PaulW/rp2040-keyboard-converter/docs/scancodes/set1.md

# Scancode Set 1 (XT)

Scancode Set 1 is the scancode design used by IBM PC and PC/XT keyboards. The designation "XT scancode set" derives from its use in the PC/XT keyboard. Set 1 continues to be used by keyboards operating in XT compatibility mode or implementing XT protocol support.

The encoding scheme: each key generates a make code when pressed and a break code when released. Break codes use the make code with bit 7 set (adding 0x80). Extended keys require multibyte sequences using E0 and E1 prefixes to encode keys not present on the original XT keyboard layout. Set 1 has been in use since the original IBM PC/XT era and remains supported in XT compatibility modes.

## Encoding Scheme

### Basic Encoding

Set 1 uses an 8-bit encoding where:

- **Bit 7 (0x80)**: Release flag
  - `0` = Key press (make code)
  - `1` = Key release (break code)
- **Bits 6-0**: Key identity (0x01-0x7F)

### Make and Break Codes

| Event | Encoding | Example (ESC key = 0x01) |
| --- | --- | --- |
| **Key Press (Make)** | `code` | `0x01` |
| **Key Release (Break)** | `code \| 0x80` | `0x81` |

This simple scheme means:

- Make code: `0x1C` (Return key pressed)
- Break code: `0x9C` (Return key released)

### Extended Keys (E0 Prefix)

The IBM Enhanced Keyboard (introduced with the IBM AT) added keys not present on the original XT keyboard: arrow keys, separate cursor movement keys (Home, End, Page Up, Page Down), and additional modifiers (Right Alt, Right Control). IBM used the E0 prefix byte to encode these "extended keys" in a separate namespace from the existing single-byte scancodes.

Extended keys use a two-byte sequence:

| Sequence | Description |
| --- | --- |
| `E0 xx` | Extended key press |
| `E0 (xx \| 0x80)` | Extended key release |

**Example: Right Control**

- Press: `E0 1D`
- Release: `E0 9D`

Extended keys include:

- Right Alt, Right Control
- Arrow keys (Up, Down, Left, Right)
- Navigation cluster (Home, End, Page Up, Page Down, Insert, Delete)
- Windows keys (E0 5B, E0 5C)
- Application key (E0 5D)
- Multimedia keys

### Pause/Break Key (E1 Prefix)

The Pause/Break key sends a 6-byte sequence entirely on key-down. There is no key-up wire event.

| Event | Sequence |
| --- | --- |
| **Pause key-down** (press only) | `E1 1D 45 E1 9D C5` (no separate key-up wire event) |
| **Break make** (Ctrl+Pause) | `E0 46` (some keyboards emit `E0 45`) |
| **Break release** (Ctrl+Pause)  | `E0 C6` (some keyboards emit `E0 C5`) |

**Important**:

- The Pause key has no separate key-release event on the wire. The full 6-byte sequence `E1 1D 45 E1 9D C5` arrives on key-down only. The converter uses `E1 1D 45` to generate a HID press and `E1 9D C5` to generate a HID release — both are derived from the single key-down burst, not from separate wire events.
- Break (Ctrl+Pause) is a standard make/release pair. Some keyboards emit `E0 45`/`E0 C5` instead of `E0 46`/`E0 C6`.

**USB HID Mapping:**

- All Pause variants map to **interface code 0x48** (USB HID Pause/Break key)
- E1 Pause: `E1 1D 45` → 0x48 press; `E1 9D C5` → 0x48 release (both from single key-down burst; no Ctrl modifier)
- E0 46 or E0 45 (Ctrl+Pause make): → 0x48 make, with Ctrl asserted in the modifier byte (Ctrl is physically held when this sequence is sent)
- E0 C6 or E0 C5 (Ctrl+Pause release): → 0x48 release, with Ctrl still in the modifier byte
- See Issue #21 for historical context on E0 mapping fixes
- Note: Some very old or non-compliant keyboards may not emit the E1 prefix for Pause
  (they instead send a bare sequence that looks like Ctrl+NumLock). Such keyboards cannot
  be reliably distinguished from intentional Ctrl+key combinations in firmware without
  introducing fragile heuristics that break other combinations. Recommended workaround:
  remap an unused physical key (for example Scroll Lock) to PAUS in your keyboard
  configuration if you need a dedicated Pause key for a non-compliant keyboard.

### Fake Shift Codes

Set 1 Print Screen scancodes include "fake shift" codes. The IBM PC XT Technical Reference documents Print Screen as involving the Shift key. The AT keyboard's Print Screen implementation uses extended key encoding (E0 prefix) and includes shift codes in the scancode sequence that do not correspond to physical Shift key presses.

Implementations must filter these fake shift codes to prevent unintended Shift key events in the output.

Set 1 Print Screen sequences include "fake shift" codes:

| Sequence | Description |
| --- | --- |
| `E0 2A E0 37` | Print Screen press (fake left shift + actual code) |
| `E0 B7 E0 AA` | Print Screen release (actual release + fake left shift release) |

**Fake shift bytes to ignore:**

- `E0 2A` - Fake Left Shift press
- `E0 AA` - Fake Left Shift release
- `E0 36` - Fake Right Shift press
- `E0 B6` - Fake Right Shift release

Modern converters should **filter out** these fake shift codes to prevent spurious Shift events.

### Self-Test Code Collision

Set 1 has a collision between self-test codes and valid scancodes. The self-test passed code `0xAA` is identical to the Left Shift break code (`0x2A | 0x80 = 0xAA`). This creates a potential for misinterpreting keyboard reset events as key releases.

**Protocol Layer Filtering:**

The collision is mitigated by protocol-layer filtering during keyboard initialisation. The protocol layer (XT, AT/PS2) consumes self-test codes before they reach the scancode processor:

- **XT Protocol**: Filters `0xAA` (BAT_PASSED) and `0xFC` (BAT_FAILED) whilst in `UNINITIALISED` state—only after receiving `0xAA` does it transition to `INITIALISED` and begin forwarding scancodes to the ring buffer (see [`src/protocols/xt/keyboard_interface.c`](../../src/protocols/xt/keyboard_interface.c))
- **AT/PS2 Protocol**: Expects `0xAA` (BAT_PASSED) in `INIT_AWAIT_SELFTEST` state—any other byte triggers a reset sequence; only after successful self-test does it transition to `INIT_READ_ID_1` and eventually `INITIALISED` (see [`src/protocols/at-ps2/keyboard_interface.c`](../../src/protocols/at-ps2/keyboard_interface.c))
- Once `INITIALISED`, all codes are forwarded unchanged to the scancode layer via the ring buffer—no protocol-layer filtering

**Scancode Layer Behaviour:**

The Set 1 scancode processor ([`src/scancodes/set1/scancode.c`](../../src/scancodes/set1/scancode.c)) does **not** filter self-test codes. It performs a range check (`if (code <= 0xD8)`) that processes all valid scancodes, including `0xAA`:

Since `0xAA` (170 decimal) is less than `0xD8` (216 decimal), it would be processed as a normal Left Shift break code if received post-initialisation. The scancode processor comment explicitly notes: _"Self-test codes (0xAA) are handled by protocol layer during initialisation"_ (see [`src/scancodes/set1/scancode.c`](../../src/scancodes/set1/scancode.c)).

The only special handling of `0xAA` in the scancode layer occurs in the E0-prefixed state, where it's filtered as a "fake shift" sequence for Print Screen (not because it's a self-test code):

```c
case E0:
    switch (code) {
        case 0x2A:
        case 0xAA:  // Filtered as fake shift, NOT as self-test code
        case 0x36:
        case 0xB6:
            // ignore fake shift
            state = INIT;
            break;
```

**Why Protocol-Layer Filtering Suffices:**

Protocol-layer filtering during initialisation is the sole mitigation for self-test code collisions. Post-initialisation, keyboards should not spontaneously send `0xAA` during normal operation. If hot-plugging occurs (not a supported scenario), the `0xAA` would indeed be misinterpreted as Left Shift break.

## State Machine

Set 1 requires a **5-state** state machine to handle all sequences:

```text
┌─────────────┐
│    INIT     │ ◄─────────────────┐
└─────┬───────┘                   │
      │                           │
      ├─[E0]──► E0 ──[code]───────┤
      │                           │
      ├─[E1]──► E1 ──[1D]──► E1_1D ──[45]──────────────────────────────────┐
      │          └───[9D]──► E1_9D ──[C5]────────────────────────────────┐ │
      │                                                                  │ │
      └─[code]───────────────────────────────────────────────────────────┘ │
                                                                           │
      ◄────────────────────────────────────────────────────────────────────┘
```

### State Descriptions

| State | Description | Next Action |
| --- | --- | --- |
| **INIT**  | Waiting for scancode | Process code or enter prefix state |
| **E0** | E0 prefix received | Process extended key, filter fake shifts |
| **E1** | E1 prefix received | Begin Pause sequence parsing |
| **E1_1D** | E1 1D received | Expect 45 (Pause make), then return to INIT |
| **E1_9D** | E1 9D received | Expect C5 (Pause release), then return to INIT |

## Key Characteristics

**What works well:**

The encoding is quite simple—release codes are just make codes with 0x80 added, which makes the state machine fairly compact at only 5 states. Single-byte scancodes are the norm, which keeps things efficient. Each byte has semantic meaning, so the protocol is self-synchronising. BIOS implementations support Set 1 widely, so compatibility's rarely an issue.

**Where it gets awkward:**

The keyspace is limited to 128 make codes (7-bit), which becomes a problem for modern keyboards with extra keys. Print Screen requires filtering out "fake shift" codes that were added for compatibility. The Pause/Break key uses an irregular sequence—6 bytes for Pause, and the break code doesn't follow the usual pattern. If you're using the XT protocol, there's no way for the host to talk back to the keyboard—it's strictly one-way communication.

## Code Range

| Range | Usage |
| --- | --- |
| `0x01-0x53` | Standard key make codes (83-key XT) |
| `0x54-0x56` | Reserved/extended make codes |
| `0x57-0x58` | F11/F12 make codes (101-key extension) |
| `0x59-0x7F` | Reserved/extended |
| `0x81-0xD3` | Standard key break codes (83-key XT, make + 0x80) |
| `0xD4-0xD6` | Reserved/extended break codes |
| `0xD7-0xD8` | F11/F12 break codes (101-key extension, make + 0x80) |
| `0xD9-0xFF` | Reserved/extended break codes |

## Special Codes

| Code | Description |
| --- | --- |
| `0xAA` | Self-test passed (BAT - Basic Assurance Test) [⚠️ Collision](#self-test-code-collision) |
| `0xE0` | Extended key prefix |
| `0xE1` | Pause/Break prefix |
| `0xEE` | Echo response (not used in XT) |
| `0xF0` | Reserved |
| `0xFA` | ACK (not used in XT) |
| `0xFC` | Self-test failed [⚠️ Collision](#self-test-code-collision) |
| `0xFE` | Resend (not used in XT) |
| `0xFF` | Error/Buffer overflow |

## Example Sequences

### Regular Key (ESC)

```yaml
Press: 01
Release: 81
```

### Extended Key (Right Arrow)

```yaml
Press: E0 4D
Release: E0 CD
```

### Print Screen (with fake shifts)

```text
Press:   E0 2A E0 37  (filter E0 2A, process E0 37)
Release: E0 B7 E0 AA  (process E0 B7, filter E0 AA)
```

### Pause/Break

```text
Pause (make):    E1 1D 45  (fires on keypress)
Pause (release): E1 9D C5  (fires immediately after, same physical press)
Break (make):    E0 46     (Ctrl+Pause down)
Break (release): E0 C6     (Ctrl+Pause up)
```

## Implementation Notes

### Processing Algorithm

```c
// Simplified Set 1 processing
switch (state) {
    case INIT:
        if (code == 0xE0) {
            state = E0;
        } else if (code == 0xE1) {
            state = E1;
        } else {
            bool is_release = (code & 0x80) != 0;
            uint8_t key = code & 0x7F;
            handle_key(key, !is_release);
        }
        break;

    case E0:
        // Filter fake shifts: 2A, AA, 36, B6
        if (code != 0x2A && code != 0xAA &&
            code != 0x36 && code != 0xB6) {
            bool is_release = (code & 0x80) != 0;
            uint8_t key = translate_e0_key(code & 0x7F);
            handle_key(key, !is_release);
        }
        state = INIT;
        break;

    case E1:
        // Pause sequence handling...
        break;
}
```

### Translation Requirements

E0-prefixed keys require translation to their logical key codes:

- Map extended scancodes to appropriate HID usage codes
- Handle duplicate keys (e.g., both Left and Right Control)
- Distinguish between main keyboard and numeric keypad keys

### Compatibility Considerations

1. **XT Protocol**: Unidirectional, no host-to-keyboard commands
2. **No LED Control**: XT keyboards have built-in LED logic, not host-controlled
3. **No Typematic Control**: Key repeat rate is keyboard-internal
4. **Self-Test Code Handling**: Protocol-layer filtering during initialisation prevents self-test code collision (see [Self-Test Code Collision](#self-test-code-collision))

## Performance Characteristics

- **Bytes per key action**: 1 byte per make/break event; 2 bytes for a standard press+release pair. Extended sequences are longer.
- **State machine complexity**: Medium (5 states)
- **Processing overhead**: Low (simple bit manipulation)
- **Memory requirements**: ~256 bytes for E0 translation table

## Keyboards Using Set 1

- IBM PC/XT keyboards (1981-1987)
- IBM Model F XT (Part 1501100, 1501105)
- Some early IBM Model M keyboards with XT interface
- Many modern mechanical keyboards in "XT mode"
- Cherry G80 series with XT interface

**Note**: XT keyboards don't respond to keyboard ID commands (0xF2) because the protocol is unidirectional (keyboard to host only).

## Source Code

- **[`scancode.h`](../../src/scancodes/set1/scancode.h)** - Set 1 processor interface
- **[`scancode.c`](../../src/scancodes/set1/scancode.c)** - State machine implementation
- **[Unified Processor](../../src/scancodes/set123/)** - Multi-set processor including Set 1

## References

- [IBM PC/XT Technical Reference Manual (1983)](http://bitsavers.org/pdf/ibm/pc/xt/)
- [IBM Personal Computer AT Technical Reference (1984)](http://bitsavers.org/pdf/ibm/pc/at/1502494_PC_AT_Technical_Reference_Mar84.pdf)
- [tmk Keyboard Wiki - XT Keyboard Protocol](https://github.com/tmk/tmk_keyboard/wiki/IBM-PC-XT-Keyboard-Protocol)
- [IBM Model F XT - VintagePC](https://www.seasip.info/VintagePC/ibm_1501105.html)

---

## Related Documentation

- [XT Protocol](../protocols/xt.md) - Protocol specification using Scancode Set 1
- [Protocols Overview](../protocols/README.md) - All supported protocols
- [Architecture](../advanced/README.md) - System architecture and scancode processing

---

**Questions or stuck on something?**
Use [GitHub Discussions](https://github.com/PaulW/rp2040-keyboard-converter/discussions) or [open an issue](https://github.com/PaulW/rp2040-keyboard-converter/issues) if you've found a problem.
