PaulW/rp2040-keyboard-converter/tools/README.md

# Development Tools

The tools in this directory handle enforcement, static analysis, and testing for the RP2040 Keyboard Converter project:

- **`lint.sh`** — fast pre-commit checks for architectural rule violations (blocking ops, IRQ safety, naming conventions, etc.)
- **`analyse.sh`** — deeper language-level analysis via Clang-Tidy and Cppcheck, run inside Docker against fully-built artefacts
- **`filter_compile_db.py`** / **`parse_compile_db.py`** — helper scripts used by `analyse.sh` to process the cmake compilation database
- **`test-enforcement.sh`** — meta-testing suite for validating the lint checks themselves

## lint.sh

This script checks source code against the architectural rules defined in `.github/copilot-instructions.md`.

### Usage

```bash
# Run locally (warnings don't fail)
./tools/lint.sh

# Run in strict mode (warnings cause failure, used in CI)
./tools/lint.sh --strict
```

### What It Checks

The script runs through nineteen different checks, each targeting a specific architectural rule:

1. **Blocking Operations** - Detects `sleep_ms()`, `sleep_us()`, `busy_wait_us()`, `busy_wait_ms()`
   - ❌ **Fails**: Any blocking call found in src/
   - 💡 **Fix**: Use time-based state machines with `to_ms_since_boot(get_absolute_time())`
   - 💡 **Suppress error**: Add `// LINT:ALLOW blocking` comment for debug-only code with IRQ protection

1. **Multicore API Usage** - Detects `multicore_launch_core1`, `multicore_fifo_*`
   - ❌ **Fails**: Any multicore API usage
   - 💡 **Fix**: This project is single-core only (Core 0) by design

1. **printf in IRQ Context** - Heuristic check for `printf` in `__isr` functions
   - ⚠️ **Warns**: Possible printf/fprintf/sprintf in interrupt handlers
   - 💡 **Fix**: Use `LOG_*` macros (allowed - designed for IRQ use) or defer logging to main loop

1. **ringbuf_reset() Usage** - Detects calls to `ringbuf_reset()`
   - ⚠️ **Warns**: Must only be called with IRQs disabled
   - 💡 **Fix**: Only use during initialisation or state machine resets
   - 💡 **Suppress warning**: Add `// LINT:ALLOW ringbuf_reset` comment on same line

1. **docs-internal/ in Repository** - Checks for committed internal docs
   - ❌ **Fails**: Any docs-internal/ files tracked by git
   - 💡 **Fix**: These are local-only, never commit them

1. **copy_to_ram Configuration** - Verifies code runs from RAM
   - ⚠️ **Warns**: `pico_set_binary_type(copy_to_ram)` not found
   - 💡 **Fix**: Add to CMakeLists.txt for timing-critical code
   - 🔧 **Runtime check**: Debug builds include `ram_check_verify()` - panics if executing from Flash

1. **IRQ-Shared Variables** - Comprehensive volatile and memory barrier analysis
   - ⚠️ **Warns**: Static variables accessed in `__isr` functions without `volatile` keyword
   - ⚠️ **Warns**: Volatile reads/writes without surrounding `__dmb()` memory barriers
   - 💡 **Fix**: Use `volatile` + `__dmb()` for IRQ/main shared data
   - 💡 **Suppress warning**: Add `// LINT:ALLOW non-volatile` or `// LINT:ALLOW barrier` with justification

1. **Tab Characters** - Enforces spaces-only indentation
   - ❌ **Fails**: Tab characters found in source files
   - 💡 **Fix**: Use 4 spaces, never tabs (run `expand -t 4 <file>` to convert)

1. **Header Guards** - Verifies `#ifndef`/`#define` guards in .h files
   - ⚠️ **Warns**: Header files missing include guards
   - 💡 **Fix**: Add `#ifndef FILENAME_H` / `#define FILENAME_H` / `#endif` pattern

1. **File Headers** - Checks for license headers
   - ⚠️ **Warns**: Source files missing GPL or MIT license headers
   - 💡 **Fix**: Add appropriate license header (see code-standards.md for template)

1. **Naming Conventions** - Detects camelCase (expects snake_case)
   - ⚠️ **Warns**: Possible camelCase function/variable names
   - 💡 **Fix**: Use snake_case (e.g., `keyboard_interface_task`, not `keyboardInterfaceTask`)

1. **Include Order** - Validates include directive organisation
   - ⚠️ **Warns**: Own header not first, or SDK headers after project headers
   - 💡 **Fix**: Order: own header → blank line → stdlib → Pico SDK → external libs → project headers

1. **Missing __isr Attribute** - Checks interrupt handler declarations
   - ⚠️ **Warns**: Functions named `*_irq_handler` without `__isr` attribute
   - 💡 **Fix**: Use `void __isr keyboard_irq_handler(void)` for interrupt handlers

1. **Compile-Time Validation** - Advisory check for `_Static_assert` and `#error`
   - ℹ️ **Info**: Reports presence of compile-time validation directives
   - 💡 **Suggestion**: Consider adding compile-time checks for constants (see code-standards.md)
   - 📝 **Note**: This is advisory-only and doesn't affect pass/fail status

1. **Protocol Setup Consistency (Ring Buffer)** - Validates keyboard protocol setup pattern
   - ⚠️ **Warns**: Missing `ringbuf_reset()` call in `keyboard_interface_setup()` (keyboard protocols only)
   - 💡 **Fix**: Add `ringbuf_reset()` before PIO/IRQ setup as part of the standard 13-step initialisation
   - 📝 **Note**: Mouse protocols excluded (direct event processing, no ring buffer)
   - 📚 **Reference**: See [Protocol Implementation Guide](../docs/development/protocol-implementation.md)

1. **Protocol Setup Consistency (PIO IRQ Dispatcher)** - Validates centralised PIO IRQ management
   - ❌ **Fails**: Direct `irq_set_priority()` calls in protocol code (deprecated pattern)
   - ⚠️ **Warns**: Missing `pio_irq_dispatcher_init()` call in protocol setup functions
   - 💡 **Fix**: Use centralised PIO IRQ dispatcher from pio_helper subsystem
     - Call `pio_irq_dispatcher_init(pio_engine.pio)` during setup
     - Call `pio_irq_register_callback(&handler_function)` to register protocol handler
     - Do NOT call `irq_set_priority()` directly in protocols (managed centrally)
   - 📝 **Note**: Ensures proper IRQ multiplexing for multi-device support (e.g., keyboard + mouse)
   - 📚 **Reference**: See [src/common/lib/pio_helper.h](../src/common/lib/pio_helper.h) for API documentation

1. **Indentation Consistency** - Enforces 4-space indentation (detects 2-space)
   - ❌ **Fails**: Files with more than 5 lines using 2-space indentation
   - 💡 **Fix**: Use 4-space indentation consistently throughout the codebase
   - 📝 **Note**: clang-format off/on blocks are excluded from this check
   - 🔧 **Reference**: See [Code Standards](../docs/development/code-standards.md#formatting-and-style) for indentation rules

1. **Trailing Whitespace** - Detects lines ending with spaces
   - ❌ **Fails**: Any `.c` or `.h` file in `src/` with any trailing whitespace
   - ❌ **Fails**: Any `.md` file in `docs/`, `tools/`, `src/`, or root with a single trailing space
   - 💡 **Fix**: Configure your editor to strip trailing whitespace on save, or run `sed -i 's/[[:space:]]*$//' <file>`
   - 📝 **Note**: Trailing whitespace causes noisy diffs and editor warnings
   - 📝 **Note**: Double trailing spaces in Markdown files are intentionally allowed — they produce a hard line break (`<br>`)

1. **Local Const Hex-Literal Variables** - Detects hex-literal magic numbers hidden in `const` variable declarations
   - ❌ **Fails**: Any `const TYPE var = 0x...` declaration inside a function body
   - 💡 **Fix**: Move the value to a file-scope `#define` in the relevant constants block
   - 📝 **Note**: `readability-magic-numbers` in clang-tidy treats `const TYPE var = LITERAL` as "introducing a named constant" and never fires on such declarations — this check closes that gap
   - 📝 **Note**: Suppress with `// LINT:ALLOW local-const-hex` and a justification comment if absolutely necessary

### Integration

- **Pre-commit**: Recommended to run before committing
- **CI**: Automatically runs in strict mode on all PRs
- **Local development**: Run periodically during development

### Example Output

```text
========================================
RP2040 Architecture Lint Checks
========================================

[1/19] Checking for blocking operations...
✓ No blocking operations found

[2/19] Checking for multicore API usage...
✓ No multicore API usage found

...

========================================
Lint Summary
========================================
✓ All checks passed!
```

### Common Issues and Fixes

#### Blocking Operations Detected

**Problem**: Code uses `sleep_ms(100)` for timing

**Fix**: Use time-based state machine
```c
// Before (blocking)
sleep_ms(100);
do_something();

// After (non-blocking)
static uint32_t start_time = 0;
static bool waiting = false;

if (!waiting) {
    start_time = to_ms_since_boot(get_absolute_time());
    waiting = true;
    return;
}

if (to_ms_since_boot(get_absolute_time()) - start_time >= 100) {
    do_something();
    waiting = false;
}
```

**Exception**: Debug-only code with explicit justification
```c
// Acceptable use case: UART debug logging with IRQ protection
if (in_irq()) {
    return !queue_full();  // Never block in IRQ
}
sleep_us(delay_us);  // LINT:ALLOW blocking - UART debug logging only, IRQ-protected, yields CPU for PIO/interrupts
```

#### printf in IRQ Context

**Problem**: `printf()` called in interrupt handler

**Fix**: Use LOG macros or defer
```c
// Before (unsafe)
void __isr keyboard_irq_handler(void) {
    printf("Key pressed\n");  // DMA conflict!
}

// After (safe)
void __isr keyboard_irq_handler(void) {
    LOG_DEBUG("Key pressed");  // IRQ-safe
}

// Or defer to main loop
static volatile bool key_pressed = false;

void __isr keyboard_irq_handler(void) {
    key_pressed = true;
    __dmb();
}

void main_loop(void) {
    if (key_pressed) {
        __dmb();
        printf("Key pressed\n");
        key_pressed = false;
    }
}
```

#### Suppressing ringbuf_reset Warnings

**Problem**: Legitimate `ringbuf_reset()` call during initialisation triggers warning

**Fix**: Add annotation comment
```c
// Legitimate use - IRQs not yet enabled during init
void keyboard_interface_init(void) {
    // ... setup code ...
    ringbuf_reset();  // LINT:ALLOW ringbuf_reset
}
```

The lint script will skip warnings for lines with the `// LINT:ALLOW ringbuf_reset` annotation.

### Runtime RAM Execution Check

Debug builds (`cmake -DCMAKE_BUILD_TYPE=Debug`) include a runtime verification that code is actually executing from SRAM:

```c
#include "ram_check.h"

int main(void) {
    ram_check_verify();  // Panics if executing from Flash (0x10000000)
                          // Passes if executing from SRAM (0x20000000)
    // ... rest of initialisation
}
```

This catches Flash execution at runtime, which complements the lint script's static check for `pico_set_binary_type(copy_to_ram)` in CMakeLists.txt.

## Testing the Tools

If you're modifying the enforcement tools themselves (not regular development), run the meta-testing suite:

```bash
./tools/test-enforcement.sh
```

This validates that lint checks detect violations correctly. See [TESTING.md](TESTING.md) for detailed scenarios and [QUICKTEST.md](QUICKTEST.md) for quick reference commands.

For regular development, just run the lint script before committing:

```bash
./tools/lint.sh && echo "✅ Ready to commit"
```

For deeper language-level analysis, run the analyser after a build:

```bash
docker compose run --rm -e KEYBOARD="modelf/pcat" analyser
```

## analyse.sh

This script runs the Debian Packaged version of [Clang 19.1.7](https://discourse.llvm.org/t/llvm-19-1-7-released/84062) and [Cppcheck 2.19.0](https://cppcheck.sourceforge.io/) against the project's source files. Running the analyser locally lets you reproduce and investigate any static-analysis findings before they appear in code review.

The analyser is invoked via the `analyser` Docker Compose service, which runs a full firmware build first and then analyses the result. Because analysis runs against the completed build artefacts — including all generated PIO header files — there are no missing-file or linking errors that you'd otherwise see if analysis ran before the build.

### Usage

```bash
# Build + analyse (recommended — uses fully built artefacts)
docker compose run --rm -e KEYBOARD="modelf/pcat" analyser

# With a different keyboard configuration
docker compose run --rm -e KEYBOARD="modelm/enhanced" analyser

# With mouse support included
docker compose run --rm -e KEYBOARD="modelm/enhanced" -e MOUSE="at-ps2" analyser
```

`KEYBOARD` selects which keyboard configuration cmake uses when building. It defaults to `modelf/pcat` if not set, which exercises the AT/PS2 protocol, HID interface, scancode processing, and Command Mode — the most common code paths.

### What It Checks

**Clang-Tidy** runs a set of checks focused on correctness and readability for embedded C11 code. C++-specific and modernise checks are disabled. The active checks are configured in [`.clang-tidy`](../.clang-tidy) at the repository root. Categories include:

- `bugprone-*` — potential logic errors, incorrect API usage, unsafe casts
- `clang-analyzer-*` — deeper static analysis: null dereferences, use-after-free, dead code
- `cert-*` — CERT C secure coding rules applicable to embedded systems
- `readability-*` — naming, clarity, and formatting (magic numbers, magic name literals disabled)

**Cppcheck 2.19.0** checks the same files for:

- `performance` — inefficient patterns
- `portability` — platform-specific assumptions
- `missingInclude` — headers that can't be resolved

Checks that fire on string-valued or date-valued defines (which can't be safely evaluated by cppcheck) are automatically filtered out by `parse_compile_db.py`.

### How It Works

The build step inside the container produces a `compile_commands.json` file alongside the normal firmware artefacts. This database records the exact compiler flags — includes, defines, architecture flags — for every source file. The analysis pipeline then uses it so both tools see exactly the same build context as the real compiler.

Three helper scripts handle the database work:

- **`filter_compile_db.py`** — strips out Pico SDK and generated entries, leaving only project source files
- **`parse_compile_db.py`** — extracts include paths, defines, and the file list from the filtered database

These are copied into the container during `docker compose build` and called by `analyse.sh` at runtime.

### Output

```text
========================================
Static Analysis
========================================

[INFO] Using existing build directory: /usr/local/builder/build-tmp
[ OK ] compile_commands.json found

[INFO] Parsing compilation database (files, includes, defines)...
  42 include dirs, 87 defines (5 skipped — complex values), 18 files

----------------------------------------
Clang-Tidy
----------------------------------------
...

----------------------------------------
Cppcheck 2.19.0
----------------------------------------
...

========================================
Analysis Summary
========================================
  clang-tidy           errors: 0   warnings: 3
  cppcheck             errors: 0   warnings: 0

RESULT: PASSED WITH WARNINGS — 3 warning(s)
```

Exit code 0 means passed (with or without warnings). Exit code 1 means at least one error was found.

### Relationship to lint.sh

These two tools are complementary, not overlapping:

| | `lint.sh` | `analyse.sh` |
|--|--|--|
| **Purpose** | Architecture & project conventions | Language-level correctness |
| **Speed** | Seconds | Minutes (full build required) |
| **Needs Docker** | No | Yes |
| **When to run** | Before every commit | When investigating findings |
| **CI** | Required on every PR | On demand |

Run `lint.sh` before committing. Run the analyser when you want to investigate a static-analysis warning or verify code quality before submitting a PR.

## filter_compile_db.py

```
python3 tools/filter_compile_db.py <input_db> <output_db> <src_prefix>
```

Filters a CMake `compile_commands.json` to entries whose `file` path starts with `src_prefix`. Without this, analysis tools would follow entries for the thousands of Pico SDK files included in a cmake project. Called by `analyse.sh`; not normally run directly.

## parse_compile_db.py

```bash
python3 tools/parse_compile_db.py <project_db> <files_out> <includes_out> <defines_out>
```

Parses the filtered compilation database and writes three output files: one source file path per line, one include directory per line, and one preprocessor define per line. Defines with string or date values (which would cause cppcheck to bail out) are filtered out automatically. Called by `analyse.sh`; not normally run directly.

## Contributing

If you're adding new lint checks, add the check logic to `lint.sh`, add corresponding test cases to `test-enforcement.sh` that verify the check detects violations correctly, document the new check in this README, and update `.github/PULL_REQUEST_TEMPLATE.md` with any relevant checklist items.

For new standalone tools, create an executable shell script (`chmod +x tools/new-tool.sh`) and document its usage here. Follow the patterns used by existing tools — colour-coded output, meaningful exit codes (0 for success, 1 for failure), and clear error messages. If the tool should run in CI, update `.github/workflows/ci.yml` accordingly.
