PaulW/rp2040-keyboard-converter/src/keyboards/modelm/1390131/README.md

# IBM Model M (101-key) Keyboard, Model 1390131

Model M (1390131)

This is the Keyboard Mapping & Configuration for the IBM Model M Keyboard, model 1390131.  This model has a US ANSI Layout.  It operates using the AT Protocol, and uses Set 2 Scancodes.

## Key Mapping

The keys can be re-assigned by updating the [keyboard.c](keyboard.c) file.  Please refer to [hid_keycodes.h](/src/common/lib/hid_keycodes.h) to list available key codes which can be mapped.  The Layers are defined and laid out in a way which matches the default key layout of the IBM Model M Keyboard.  I do intend on slightly updating the layout, and this will be made clear when I commit that change.

Please note, that some keys require the use of the Fn Modifier Key to be pressed (by default, this is mapped to Right-Alt).  Keys mapped with dual values also represent pressing Shift Modifier.

Right-Ctrl is mapped to LGUI (Windows Key or Command Key)

| Key on Keyboard | Modifier Mapping |
|---|---|
| CapsLock | Menu |

_* Mapping may differ on Windows PC, I've not tested this_

All Layouts are set as if the keyboard is set to British PC (as per my Mac)

Layout Toggle
