PaulW/rp2040-keyboard-converter/docs/development/protocol-implementation.md

# Protocol Implementation Guide

If you're adding a new keyboard or mouse protocol to the converter, there's a standard pattern that all protocol implementations follow. This isn't enforced by the build system—it's more of a convention that's emerged from the existing implementations. Following this pattern makes the code easier to understand and maintains consistency across the codebase.

This guide covers the setup sequence for protocol implementations. If you're adding keyboard support for an existing protocol, you probably want the [Adding Keyboards Guide](adding-keyboards.md) instead.

---

## Understanding Protocol Setup

Each protocol has its own `keyboard_interface_setup()` function in `src/protocols/<protocol>/keyboard_interface.c`. If the protocol supports mice, there will also be a `mouse_interface_setup()` function in `mouse_interface.c`. Whilst the specific details vary according to what each protocol needs, they all follow the same basic pattern. This isn't by accident—the pattern ensures each protocol initialises its resources in the correct order and handles errors consistently.

The pattern matters because:

- PIO resources are limited (2 PIOs, 4 state machines each)
- Ring buffer must be clean before use
- IRQ handlers need proper priority configuration
- LED state should reflect the actual hardware state
- Error conditions need consistent handling

Things can go wrong if you deviate from this pattern. For instance, if you set up the IRQ handler before clearing the ring buffer, you might process stale data from a previous session. If you don't initialise the LED state, the indicator might show ready when the keyboard isn't actually initialised yet.

---

## Standard Setup Sequence

Here's the standard pattern all protocols follow, in order:

### 1. LED Initialisation

Set the device-specific ready state to false and update the status LED. This happens before anything else because you want the LED to show the actual state — the device isn't ready yet, so don't indicate that it is. Keyboard protocols set `kb_ready`; the mouse protocol sets `mouse_ready`.

```c
// Keyboard example
#ifdef CONVERTER_LEDS
  converter.state.kb_ready = 0;
  update_converter_status();
#endif

// Mouse example
#ifdef CONVERTER_LEDS
  converter.state.mouse_ready = 0;
  update_converter_status();
#endif
```

The `#ifdef` is there because LED support is optional (controlled by `CONVERTER_LEDS` define). If LEDs aren't configured, the code doesn't include the LED library at all, which saves a bit of memory.

### 2. Ring Buffer Reset

Next, clear any stale data from the ring buffer. The buffer might contain leftover scancodes from a previous session (if the converter was reset but the keyboard wasn't power-cycled), so you need a clean slate before starting.

```c
ringbuf_reset();  // LINT:ALLOW ringbuf_reset
```

The `LINT:ALLOW` annotation tells the lint checker this is intentional. Normally, calling `ringbuf_reset()` whilst IRQs are enabled would be flagged as an error (it's not safe—the IRQ handler might be writing to the buffer). Here it's fine because we're in the setup function before IRQs are enabled.

### 3. PIO Instance Allocation

Now find an available PIO instance that has enough instruction memory for your protocol's program. The RP2040 has two PIO blocks (PIO0 and PIO1), each with 32 instruction memory slots. The helper function searches both and returns the first one with enough space.

```c
pio_engine_t pio_engine = claim_pio_and_sm(&pio_interface_program);
if (pio_engine.pio == NULL) {
  LOG_ERROR("No PIO available for AT/PS2 Keyboard Interface Program\n");
  return;
}
```

The `claim_pio_and_sm()` helper function handles PIO allocation, state machine claiming, and program loading atomically. It tries PIO0 first, then falls back to PIO1 if needed. If both PIO blocks are exhausted, it returns a struct with `pio = NULL`.

This atomic allocation ensures no partial failures—you either get a complete working PIO engine (instance + state machine + loaded program) or nothing. The error message should identify which protocol failed (helpful when debugging multi-protocol builds or when system resources are exhausted).

### 4. PIO Engine Structure

The `pio_engine_t` struct returned by `claim_pio_and_sm()` contains everything needed to use the PIO hardware:

```c
typedef struct {
    PIO pio;    // PIO instance (pio0/pio1), or NULL on failure
    int sm;     // State machine (0-3), or -1 on failure
    int offset; // Program memory offset (0-31), or -1 on failure
} pio_engine_t;
```

All protocol implementations declare this as a static variable with explicit initialisation:

```c
static pio_engine_t pio_engine = {.pio = NULL, .sm = -1, .offset = -1};
```

The struct stores `sm` and `offset` as signed values so the project can use `-1` as a clear sentinel for "unallocated/invalid". Protocol code must validate allocation succeeded before passing these values to Pico SDK helpers that take `uint` parameters.

### 5. Why Atomic Allocation?

The previous pattern required three separate steps:

```c
// Old pattern (deprecated)
PIO pio = find_available_pio(&program);  // Step 1: Check space
if (pio == NULL) return;
int sm = pio_claim_unused_sm(pio, false);  // Step 2: Claim SM
if (sm < 0) return;
int offset = pio_add_program(pio, &program);  // Step 3: Load program
```

This created opportunities for partial failures and duplicated error handling across all protocols. The atomic approach reduces error handling to a single NULL check and avoids partial allocations:

```c
// Current pattern
pio_engine_t pio_engine = claim_pio_and_sm(&program);
if (pio_engine.pio == NULL) return;  // Single error check
// Ready to use: pio_engine.pio, pio_engine.sm, pio_engine.offset
```

Benefits:

- Single error check instead of three
- No partial allocation state
- Automatic fallback from PIO0 to PIO1
- Consistent pattern across all protocols
- Type safety through struct encapsulation

### 6. Pin Assignment

Store the GPIO pin number(s) for the protocol. This varies by protocol needs:

```c
// Most protocols: single data pin
keyboard_data_pin = data_pin;

// Amiga protocol: separate clock and data pins (must be adjacent)
keyboard_data_pin = data_pin;
keyboard_clock_pin = data_pin + 1;
```

The Amiga protocol has a specific requirement where the clock pin must be immediately after the data pin (a constraint of how the PIO program is written). Other protocols might have different requirements—document them clearly if your protocol has specific pin relationships.

### 7. Clock Divider Calculation

Calculate the PIO clock divider based on your protocol's timing requirements. The helper function converts a microsecond timing value into the divider ratio needed by the PIO hardware.

```c
float clock_div = calculate_clock_divider(ATPS2_TIMING_CLOCK_MIN_US);
```

The timing constant should be defined in your protocol's header file, not hardcoded here. This makes it easier to adjust timing if needed and documents what the value represents.

### 8. PIO Program Initialisation

Initialise the state machine with your program. This sets up the PIO hardware: configures pins, sets the clock divider, loads the initial state, and prepares the state machine to run.

```c
pio_interface_program_init(pio_engine.pio, pio_engine.sm, pio_engine.offset, data_pin, clock_div);
```

The init function is generated by `pioasm` (the PIO assembler) and is specific to your protocol's `.pio` file. It knows how to configure the state machine for your particular program's requirements. The function accepts `uint` parameters for `sm` and `offset`, but we pass `int` values from the `pio_engine` struct. This implicit conversion is safe because we've validated that allocation succeeded (the values are non-negative).

### 9. PIO IRQ Dispatcher Initialisation

Initialise the centralised PIO IRQ dispatcher for this PIO instance. This sets up a shared interrupt handler that can multiplex callbacks from multiple protocols (e.g., keyboard + mouse on the same PIO).

```c
pio_irq_dispatcher_init(pio_engine.pio);
```

The dispatcher manages IRQ priority (set to 0x00 - highest priority) and provides callback registration for protocol handlers. This centralised approach prevents conflicts when multiple devices share the same PIO instance.

**Important:** The dispatcher is designed to be called multiple times safely (e.g., once during keyboard setup, again during mouse setup for the same PIO). Subsequent calls are idempotent—they detect existing configuration and return immediately without reconfiguring the IRQ.

### 10. IRQ Handler Registration

Register your protocol's interrupt handler as a callback with the PIO IRQ dispatcher. The handler will be called when the PIO raises an interrupt (typically when it receives a complete scancode).

```c
pio_irq_register_callback(&keyboard_input_event_handler);
```

The dispatcher supports up to 4 callbacks total (global registry) and only one PIO instance per session. Multiple protocols can share a single PIO (e.g., AT/PS2 keyboard + mouse), and handlers are called sequentially from the shared dispatcher.

**Error handling:** If registration fails (e.g., all 4 callback slots full), the function returns `false` and logs an error. Always call `release_pio_and_sm()` to free the already-claimed PIO resources before returning:

```c
if (!pio_irq_register_callback(&keyboard_input_event_handler)) {
    LOG_ERROR("Protocol: Failed to register IRQ callback\n");
    release_pio_and_sm(&pio_engine, &keyboard_interface_program);
    return;
}
```

`release_pio_and_sm()` is the complement to `claim_pio_and_sm()`. It disables the state machine, clears both FIFOs, unclaims the SM, removes the program from instruction memory, and resets all engine fields to the failure sentinel (`NULL`/`-1`/`-1`). It is safe to call when `engine->pio` is `NULL` (no-op), which means it can be used unconditionally in error paths.

**Note:** `pio_irq_register_callback()` also enables the PIO IRQ internally on first callback registration, after a `__dmb()` memory barrier ensures the callback is visible to the IRQ handler. There is no separate `irq_set_enabled()` call in protocol setup code — it happens inside the helper.

### 11. Logging

Update the LED/status indicator and log confirmation that setup completed. Include relevant details like which PIO instance and state machine were allocated, and any protocol-specific parameters.

The `LOG_INFO()` call and LED/status update always belong here — they confirm that hardware setup completed and provide an audit trail in the UART output.

The ready-flag assignment (`kb_ready = 1` / `converter.state.mouse_ready = 1`) is protocol-dependent. Set it here only if the protocol reaches its ready state synchronously during setup. Protocols that become ready only after runtime or ISR initialisation (e.g. after receiving an acknowledgement or self-test response) should set the flag from that path instead — for example, from `keyboard_event_processor()` or the equivalent post-initialisation handler.

```c
// Keyboard example — ready flag set here only for synchronous-init protocols
kb_ready = 1;  // For async-init protocols, set this from keyboard_event_processor() instead
update_keyboard_ready_led();
LOG_INFO("PIO%d SM%d Interface program loaded at offset %d with clock divider of %.2f\n",
         (pio_engine.pio == pio0 ? 0 : 1), pio_engine.sm, pio_engine.offset, clock_div);

// Mouse example — ready flag set here only for synchronous-init protocols
converter.state.mouse_ready = 1;  // For async-init protocols, set this from the event processor instead
update_converter_status();
LOG_INFO("PIO%d SM%d Mouse Interface program loaded at offset %d with clock divider of %.2f\n",
         (pio_engine.pio == pio0 ? 0 : 1), pio_engine.sm, pio_engine.offset, clock_div);
```

This appears in the UART debug output and helps verify the protocol initialised correctly. It's particularly useful when debugging resource allocation issues or when multiple protocols are loaded simultaneously.

---

## Pattern Variations

Whilst all keyboard protocols follow this basic structure, there are legitimate reasons for variations:

### Mouse vs. Keyboard Setup

The AT/PS2 protocol supports both keyboards and mice on separate hardware lines. The mouse setup in `mouse_interface_setup()` follows a similar pattern with one critical difference:

**Mouse does NOT use the ring buffer.** Unlike keyboards which queue scancodes through the ring buffer for processing in the main loop, mice process data packets directly in the IRQ context via `mouse_event_processor()`. This means:

```c
void mouse_interface_setup(uint data_pin) {
  // 1. LED initialisation
  #ifdef CONVERTER_LEDS
    converter.state.mouse_ready = 0;
    update_converter_status();
  #endif

  // 2. NO ringbuf_reset() - mouse doesn't use ring buffer

  // 3. Claim PIO resources atomically
  pio_engine_t pio_engine = claim_pio_and_sm(&pio_interface_program);
  if (pio_engine.pio == NULL) {
    LOG_ERROR("No PIO resources available for mouse\n");
    return;
  }
  // ... rest of setup continues with pio_engine.pio, pio_engine.sm, pio_engine.offset
}
```

**Why this difference?**

- Keyboard: Multibyte scancode sequences need buffering (E0 prefixes, Pause key sequences)
- Mouse: Fixed packet format (3-4 bytes), processed as complete packets in IRQ handler
- Mouse: HID reports sent immediately after packet validation

The mouse still follows the same resource allocation pattern (atomic PIO/SM/program allocation via `claim_pio_and_sm()`), just without the ring buffer reset step.

### Error Handling Approach

All protocols use the atomic PIO resource allocation pattern implemented by `claim_pio_and_sm()`. This function attempts to allocate a PIO instance, state machine, and program memory atomically, trying PIO0 first and falling back to PIO1 if necessary.

```c
pio_engine_t pio_engine = claim_pio_and_sm(&program);
if (pio_engine.pio == NULL) {
  LOG_ERROR("No PIO resources available\n");
  return;
}
```

If a later setup step fails after PIO resources have been claimed (e.g., IRQ callback registration fails because all callback slots are full), release the already-claimed resources before returning using `release_pio_and_sm()`:

```c
if (!pio_irq_register_callback(&handler)) {
  LOG_ERROR("Failed to register IRQ callback\n");
  release_pio_and_sm(&pio_engine, &program);  // Release already-claimed resources
  return;
}
```

`release_pio_and_sm()` is the complement to `claim_pio_and_sm()` — it disables the state machine, clears both FIFOs, unclaims the SM, removes the program from instruction memory, and resets all engine fields to the failure sentinel. It is safe to call when `engine->pio` is `NULL` (no-op).

The `pio_engine_t` struct always exists; `pio_engine.pio == NULL` (with `sm`/`offset` set to -1) indicates complete failure. Together, the pair of helpers provides:

- Handles PIO selection (pio0 vs pio1) automatically with fallback
- Eliminates partial allocation failures (no allocated SM without program space)
- Provides clean single-point error handling (one NULL check covers all failure cases)
- Returns complete working resources or nothing
- Type-safe through struct encapsulation

Used across protocol implementations under `src/protocols/` and the WS2812 helper under `src/common/lib/ws2812/`.

### Pin Requirements

**Single pin:**

```c
keyboard_data_pin = data_pin;
```

**Adjacent pins:**

```c
keyboard_data_pin = data_pin;
keyboard_clock_pin = data_pin + 1;  // Must be adjacent
```

Document any pin relationship requirements clearly in your protocol's README. If pins must be adjacent, state why (usually it's a PIO program requirement). If there's flexibility, mention that too.
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
