PaulW/rp2040-keyboard-converter/docs/features/layers.md

# Keyboard Layers

Layers let you access different sets of key functions without adding physical keys to your keyboard. Think of them as transparent overlays—you activate a layer and suddenly the same physical keys do different things. Press a key on your numpad and it might be a '7', or it might be HOME, depending on which layer is active.

This isn't a new concept. Keyboards already use a form of layering—the Shift key is one example. Hold Shift and the '2' key sends '@' instead of '2'. You've got two layers there: the base layer with numbers, and the shifted layer with symbols. The converter just extends this concept further, giving you access to additional layers for functions, media controls, or alternative layouts.

---

## What Layers Are For
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
