PaulW/rp2040-keyboard-converter/src/hid_interface.c

/*
 * This file is part of Model-F 5170 Converter.
 *
 * Copyright 2023 Paul Bramhall (paulwamp@gmail.com)
 *
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
 * You should have received a copy of the GNU General Public License
 * along with Model-F 5170 Converter.
 * If not, see <https://www.gnu.org/licenses/>.
 */

#include "hid_interface.h"

#include <stdio.h>

#include "bsp/board.h"
#include "hid_keycodes.h"
#include "keymaps/keymaps.h"
#include "lock_leds.h"
#include "pico/bootrom.h"
#include "tusb.h"
#include "usb_descriptors.h"

static hid_keyboard_report_t keyboard_report;

enum {
  USAGE_PAGE_KEYBOARD = 0x0,
  USAGE_PAGE_CONSUMER = 0xC,
};

// Output the HID Report sent to the host.  Purely for debugging.
static void hid_print_report(void) {
  printf("[HID-REPORT] ");
  uint8_t* p = (uint8_t*)&keyboard_report;
  for (uint i = 0; i < sizeof(keyboard_report); i++) {
    printf("%02X ", *p++);
  }
  printf("\n");
}

// Add a new keycode to the HID report upon keypress.
static bool hid_keyboard_add_key(uint8_t key) {
  if (IS_MOD(key)) {
    if ((keyboard_report.modifier & (uint8_t)(1 << (key & 0x7))) == 0) {
      keyboard_report.modifier |= (uint8_t)(1 << (key & 0x7));
      return true;
    }
    return false;
  }

  int empty = -1;
  for (size_t i = 0; i < 6; i++) {
    if (keyboard_report.keycode[i] == key) return false;
    if (empty == -1 && keyboard_report.keycode[i] == 0) empty = (int)i;
  }
  if (empty != -1) {
    keyboard_report.keycode[empty] = key;
    return true;
  }
  return false;
}

// Remove keycode from HID report when key is released.
static bool hid_keyboard_del_key(uint8_t key) {
  if (IS_MOD(key)) {
    if ((keyboard_report.modifier & (uint8_t)(1 << (key & 0x7))) != 0) {
      keyboard_report.modifier &= (uint8_t) ~(1 << (key & 0x7));
      return true;
    }
    return false;
  }

  for (size_t i = 0; i < 6; i++) {
    if (keyboard_report.keycode[i] == key) {
      keyboard_report.keycode[i] = 0;
      return true;
    }
  }
  return false;
}

// Handle input reports for the keyboard usage page
// Only if the Keyboard Report changes do we then call `hid_send_report_with_retry`
// PS2 Keyboards send typematic key presses repetatively, yet with HID devices, we
// only want to send a report for each Key Press/Release Event.  The host will handle
// all typematic events itself.
static void handle_keyboard_report(uint8_t code, bool make) {
  // uint8_t key = (uint8_t)(code & 0xFF);
  if (IS_KEY(code) || IS_MOD(code)) {
    bool report_modified = false;
    if (make) {
      report_modified = hid_keyboard_add_key(code);
    } else {
      report_modified = hid_keyboard_del_key(code);
    }

    // Check for any Macro Combinations here
    if (keymap_is_action_key_pressed()) {
      if (SUPER_MACRO_INIT(keyboard_report.modifier)) {
        printf("Macro Modifiers HOLD\n");
        uint8_t macro_key = MACRO_KEY_CODE(code);
        if (macro_key == KC_BOOT) {
          // Initiate Bootloader
          printf("[INFO] Initiate Bootloader\n");
          // Reboot into Bootloader
          reset_usb_boot(0, 0);
        }
      }
    }

    if (report_modified) {
      bool res = tud_hid_n_report(ITF_NUM_KEYBOARD, REPORT_ID_KEYBOARD, &keyboard_report, sizeof(keyboard_report));
      if (!res) {
        printf("[ERR] KEYBOARD HID REPORT FAIL\n");
        hid_print_report();
      }
    }
  } else if (IS_CONSUMER(code)) {
    uint16_t usage;
    if (make) {
      usage = CODE_TO_CONSUMER(code);
    } else {
      usage = 0;
    }
    bool res = tud_hid_n_report(ITF_NUM_CONSUMER_CONTROL, REPORT_ID_CONSUMER_CONTROL, &usage, sizeof(usage));
    if (!res) {
      printf("[ERR] Consumer Report Failed: 0x%04X\n", usage);
    }
  }
}

// Called when character data exists in the ringbuffer from the main processing loop.
// Handles keycodes sent to it, and translates these to Scancode Set 3 and then sending
// a new HID report to the host to signal key press/release.
int8_t keyboard_process_key(uint8_t code) {
  static enum {
    INIT,
    F0,
    E0,
    E0_F0,
    E1,
    E1_14,
    E1_F0,
    E1_F0_14,
    E1_F0_14_F0
  } state = INIT;

  switch (state) {
    case INIT:

      switch (code) {
        case 0xE0:
          state = E0;
          break;
        case 0xF0:
          state = F0;
          break;
        case 0xE1:
          state = E1;
          break;
        case 0x00 ... 0x7F:
        case 0x83:  // F7
        case 0x84:  // SysReq / Alt'd PrintScreen
          handle_keyboard_report(keymap_get_key_val(code, true), true);
          break;
        case 0xAA:  // Self-test passed
        case 0xFC:  // Self-test failed
        default:    // unknown codes
          printf("[DBG] !INIT! (0x%02X)\n", code);
          return -1;
      }
      break;

    case F0:  // Break code
      switch (code) {
        case 0x00 ... 0x7F:
        case 0x83:  // F7
        case 0x84:  // SysReq
          state = INIT;
          handle_keyboard_report(keymap_get_key_val(code, false), false);
          break;
        default:
          state = INIT;
          printf("[DBG] !F0! (0x%02X)\n", code);
          return -1;
      }
      break;

    case E0:  // E0-Prefixed
      switch (code) {
        case 0x12:  // to be ignored
        case 0x59:  // to be ignored
          state = INIT;
          break;
        case 0xF0:
          state = E0_F0;
          break;
        default:
          state = INIT;
          if (code < 0x80) {
            handle_keyboard_report(keymap_get_key_val(code | 0x80, true), true);
          } else {
            printf("[DBG] !E0! (0x%02X)\n", code);
            return -1;
          }
      }
      break;

    case E0_F0:  // Break code of E0-prefixed
      switch (code) {
        case 0x12:  // to be ignored
        case 0x59:  // to be ignored
          state = INIT;
          break;
        default:
          state = INIT;
          if (code < 0x80) {
            handle_keyboard_report(keymap_get_key_val(code | 0x80, false), false);
          } else {
            printf("!E0_F0! (0x%02X)\n", code);
            return -1;
          }
      }
      break;

    case E1:  // E1-Prefixed
      switch (code) {
        case 0x14:
          state = E1_14;
          break;
        case 0xF0:
          state = E1_F0;
          break;
        default:
          state = INIT;
          printf("[DBG] !E1! (0x%02X)\n", code);
          return -1;
      }
      break;

    case E1_14:  // E1-prefixed 14
      switch (code) {
        case 0x77:  // Pause
          state = INIT;
          handle_keyboard_report(keymap_get_key_val(code | 0x80, true), true);
          break;
        default:
          state = INIT;
          printf("[DBG] !E1_14! (0x%02X)\n", code);
          return -1;
      }
      break;

    case E1_F0:  // Break code of E1-prefixed
      switch (code) {
        case 0x14:
          state = E1_F0_14;
          break;
        default:
          state = INIT;
          printf("[DBG] !E1_F0! (0x%02X)\n", code);
          return -1;
      }
      break;

    case E1_F0_14:  // Break code of E1-prefixed 14
      switch (code) {
        case 0xF0:  // Pause
          state = E1_F0_14_F0;
          break;
        default:
          state = INIT;
          printf("[DBG] !E1_F0_14! (0x%02X)\n", code);
          return -1;
      }
      break;

    case E1_F0_14_F0:  // Break code of E1-prefixed 14
      switch (code) {
        case 0x77:  // Pause
          state = INIT;
          handle_keyboard_report(keymap_get_key_val(code | 0x80, false), false);
          break;
        default:
          state = INIT;
          printf("[DBG] !E1_F0_14_F0! (0x%02X)\n", code);
          return -1;
      }
      break;

    default:
      state = INIT;
  }
  return 0;
}

// Invoked when received GET_REPORT control request
// Application must fill buffer report's content and return its length.
// Return zero will cause the stack to STALL request
uint16_t tud_hid_get_report_cb(uint8_t instance, uint8_t report_id, hid_report_type_t report_type, uint8_t* buffer, uint16_t reqlen) {
  // TODO not Implemented
  (void)instance;
  (void)report_id;
  (void)report_type;
  (void)buffer;
  (void)reqlen;

  return 0;
}

// Invoked when received SET_REPORT control request or
// received data on OUT endpoint ( Report ID = 0, Type = 0 )
void tud_hid_set_report_cb(uint8_t instance, uint8_t report_id, hid_report_type_t report_type, uint8_t const* buffer, uint16_t bufsize) {
  (void)buffer;

  if (instance != ITF_NUM_KEYBOARD) return;

  if (report_type == HID_REPORT_TYPE_OUTPUT) {
    // Set keyboard LED e.g Capslock, Numlock etc...
    if (report_id == REPORT_ID_KEYBOARD) {
      // bufsize should be (at least) 1
      if (bufsize < 1) return;
      set_lock_values_from_hid(buffer[0]);
    }
  }
}

// Public function which sets up the tinyusb stack
void hid_device_setup(void) {
  board_init();
  tusb_init();
}
