PaulW/rp2040-keyboard-converter/src/protocols/xt/interface.c

/*
 * This file is part of RP2040 Keyboard Converter.
 *
 * Copyright 2023 Paul Bramhall (paulwamp@gmail.com)
 *
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
 * You should have received a copy of the GNU General Public License
 * along with RP2040 Keyboard Converter.
 * If not, see <https://www.gnu.org/licenses/>.
 */

#include "interface.h"

#include <math.h>

#include "bsp/board.h"
#include "config.h"
#include "hardware/clocks.h"
#include "interface.pio.h"
#include "pio_helper.h"
#include "ringbuf.h"
#include "scancode.h"

#ifdef CONVERTER_LEDS
#include "led_helper.h"
#endif

uint keyboard_sm = 0;
uint offset = 0;
PIO keyboard_pio = pio1;

static enum {
  UNINITIALISED,
  INITIALISED,
} keyboard_state = UNINITIALISED;

void keyboard_pio_restart() {
  // Restart the XT PIO State Machine
  printf("[DBG] Resetting State Machine and Keyboard (Offset: 0x%02X)\n", offset);
  keyboard_state = UNINITIALISED;
  pio_sm_drain_tx_fifo(keyboard_pio, keyboard_sm);
  pio_sm_clear_fifos(keyboard_pio, keyboard_sm);
  pio_sm_restart(keyboard_pio, keyboard_sm);
  pio_sm_exec(keyboard_pio, keyboard_sm, pio_encode_jmp(offset));
  printf("[DBG] State Machine Restarted\n");
}

static void keyboard_event_processor(uint8_t data_byte) {
  switch (keyboard_state) {
    case UNINITIALISED:
      if (data_byte == 0xAA) {
        printf("[DBG] Keyboard Self-Test Passed\n");
        keyboard_state = INITIALISED;
      } else {
        printf("[ERR] Keyboard Self-Test Failed: 0x%02X\n", data_byte);
        keyboard_pio_restart();
        keyboard_state = UNINITIALISED;
      }
      break;
    case INITIALISED:
      if (!ringbuf_is_full()) ringbuf_put(data_byte);
  }
#ifdef CONVERTER_LEDS
  update_converter_status(keyboard_state == INITIALISED ? 1 : 2);
#endif
}

// IRQ Event Handler used to read keycode data from the XT Keyboard
// and ensure relevant code is valid when checking against relevant check bits.
static void __isr keyboard_input_event_handler() {
  io_ro_32 data_cast = keyboard_pio->rxf[keyboard_sm] >> 23;
  uint16_t data = (uint16_t)data_cast;

  // Extract the Start Bit.
  uint8_t start_bit = data & 0x1;
  uint8_t data_byte = (uint8_t)((data_cast >> 1) & 0xFF);

  if (start_bit != 1) {
    printf("[ERR] Start Bit Validation Failed: start_bit=%i\n", start_bit);
    keyboard_pio_restart();
    return;
  }
  keyboard_event_processor(data_byte);
}

void keyboard_interface_task() {
  if (keyboard_state == INITIALISED) {
    // This portion helps with Lock LED changes.  We only get here once the keyboard has initialised.

    if (!ringbuf_is_empty()) {
      if (tud_suspended()) {
        // Wake up host if we are in suspend mode
        // and REMOTE_WAKEUP feature is enabled by host
        tud_remote_wakeup();
      } else {
        if (tud_hid_ready()) {
          uint32_t status = save_and_disable_interrupts();  // disable IRQ
          int c = ringbuf_get();                            // critical_section
          restore_interrupts(status);
          if (c != -1) {
            process_scancode((uint8_t)c);
          }
        }
      }
    }
  } else {
    // This portion helps with initialisation of the keyboard.
    static uint8_t detect_stall_count = 0;
    static uint32_t detect_ms = 0;
    // if ((gpio_get(DATA_PIN) == 1) && (gpio_get(DATA_PIN + 1) == 1)) {
    //   printf("[DBG] Keyboard Initialised (BAT OK)!\n");
    //   keyboard_state = INITIALISED;
    // }
    if (board_millis() - detect_ms > 200) {
      detect_ms = board_millis();
      // int pin_state = gpio_get(DATA_PIN + 1);
      if (gpio_get(DATA_PIN + 1) == 1) {
        if (detect_stall_count < 5) {
          detect_stall_count++;
          printf("[DBG] Keyboard detected, awaiting ACK (%i/5 attempts)\n", detect_stall_count);
        } else {
          printf("[DBG] Keyboard detected, but no ACK received!\n");
          printf("[DBG] Requesting keyboard reset\n");
          keyboard_pio_restart();
          detect_stall_count = 0;
        }
      } else if (keyboard_state == UNINITIALISED) {
        printf("[DBG] Awaiting keyboard detection. Please ensure a keyboard is connected.\n");
        detect_stall_count = 0;
      }
#ifdef CONVERTER_LEDS
      update_converter_status(keyboard_state == INITIALISED ? 1 : 2);
#endif
    }
  }
}

// Public function to initialise the XT PIO interface.
void keyboard_interface_setup(uint data_pin) {
#ifdef CONVERTER_LEDS
  update_converter_status(2);  // Always reset Converter Status here
#endif

  // First we need to determine which PIO to use for the Keyboard Interface.
  // To do this, we check each PIO to see if there is space to load the Keyboard Interface program.
  // If there is space, we claim the PIO and load the program.  If not, we continue to the next PIO.
  // We can call `pio_can_add_program` to check if there is space for the program.
  // `find_available_pio` is a helper function that will check both PIO0 and PIO1 for space.
  // If the function returns NULL, then there is no space available, and we should return.

  keyboard_pio = find_available_pio(&keyboard_interface_program);
  if (keyboard_pio == NULL) {
    printf("[ERR] No PIO available for Keyboard Interface Program\n");
    return;
  }

  // Now we can claim the PIO and load the program.
  keyboard_sm = (uint)pio_claim_unused_sm(keyboard_pio, true);
  offset = pio_add_program(keyboard_pio, &keyboard_interface_program);

  // Define the IRQ for the PIO State Machine.
  // This should either be set to PIO0_IRQ_0 or PIO1_IRQ_0 depending on the PIO used.
  uint pio_irq = keyboard_pio == pio0 ? PIO0_IRQ_0 : PIO1_IRQ_0;

  // Define the Polling Inteval for the State Machine.
  // The XT Protocol runs at a clock speed of around 31kHz due to the clock
  // cycle of 12.5us LOW and 20us HIGH (32.5us total) per Clock Cycle.
  // There are a total maximum of 11 data bits we need to read per clock, due to
  // the possibility of a double-start bit on Genuine XT Keyboards.  XT Clone Keyboards
  // will only ever send a single start bit, but we need to be able to handle both.
  // As such, we set the polling interval to the duration of the HIGH clock cycle (20us),
  // but ensure we have 11 SM cycles per clock cycle to ensure we operate at a high enough
  // clock speed to ensure we can capture the first start bit if we are receiving a double,
  // as this does need detecting within 5us of clock going LOW.

  int polling_interval_us = 20;
  int cycles_per_clock = 11;

  // Get base clock speed of RP2040.  This should always equal 125MHz, but we will check anyway.
  float rp_clock_khz = 0.001 * clock_get_hz(clk_sys);

  printf("[INFO] RP2040 Clock Speed: %.0fKHz\n", rp_clock_khz);
  printf("[INFO] Interface Polling Interval: %dus\n", polling_interval_us);
  float polling_interval_khz = 1000 / polling_interval_us;
  printf("[INFO] Interface Polling Clock: %.0fkHz\n", polling_interval_khz);
  // Always round clock_div to prevent jitter by having a fractional divider.
  float clock_div = roundf((rp_clock_khz / polling_interval_khz) / cycles_per_clock);
  printf("[INFO] Clock Divider based on %d SM Cycles per Keyboard Clock Cycle: %.2f\n", cycles_per_clock, clock_div);
  printf("[INFO] Effective SM Clock Speed: %.2fkHz\n", (float)(rp_clock_khz / clock_div));

  keyboard_interface_program_init(keyboard_pio, keyboard_sm, offset, data_pin, clock_div);

  printf("[INFO] PIO%d SM%d Interface program loaded at offset %d with clock divider of %.2f\n", (keyboard_pio == pio0 ? 0 : 1), keyboard_sm, offset, clock_div);

  irq_set_exclusive_handler(pio_irq, &keyboard_input_event_handler);
  irq_set_enabled(pio_irq, true);
}
